niiccoo2/EINK-Phone/pic/4in2_Scale_2.bmp

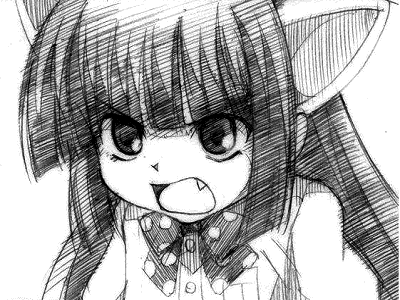
pic/4in2_Scale_2.bmp
