niiccoo2/EINK-Phone/pic/4.2 m.bmp

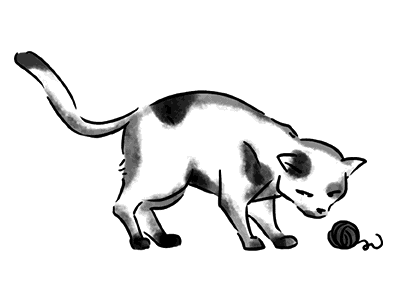
pic/4.2 m.bmp
