niiccoo2/EINK-Phone/pic/4.2-B.bmp

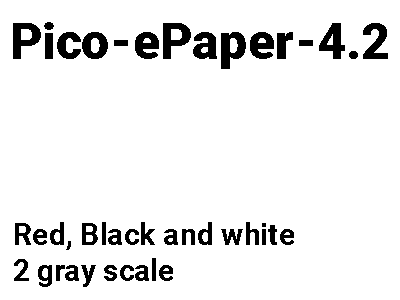
pic/4.2-B.bmp
