niiccoo2/EINK-Phone/pic/4.2-R.bmp

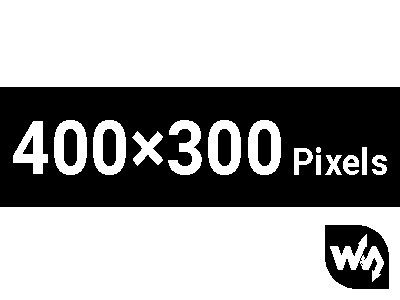
pic/4.2-R.bmp
