niiccoo2/EINK-Phone/pic/4in01-2.bmp

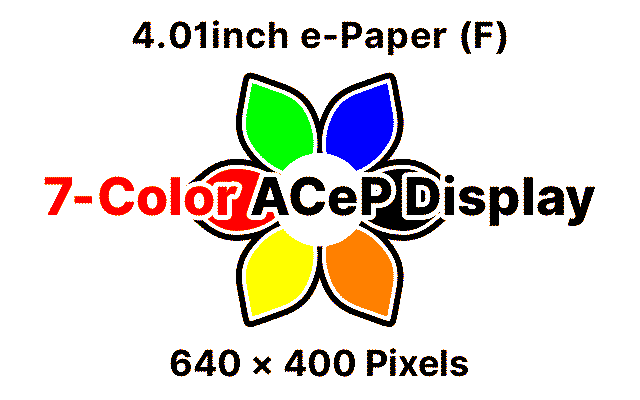
pic/4in01-2.bmp
