niiccoo2/EINK-Phone/pic/4in01-3.bmp

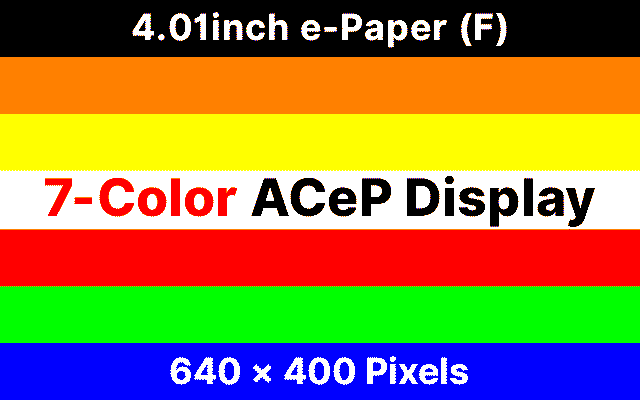
pic/4in01-3.bmp
