niiccoo2/EINK-Phone/pic/4in01-4.bmp

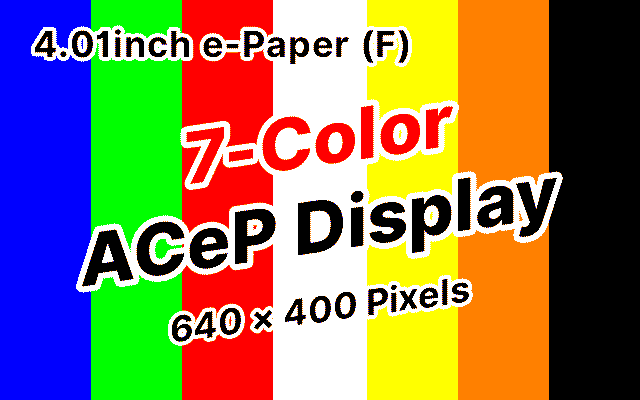
pic/4in01-4.bmp
