niiccoo2/EINK-Phone/pic/4in01f1.bmp

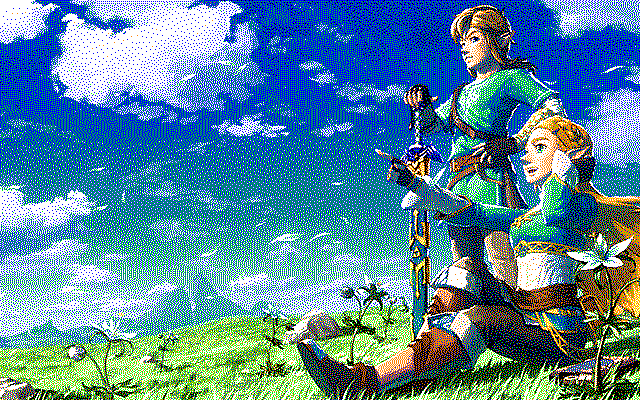
pic/4in01f1.bmp
