niiccoo2/EINK-Phone/pic/4in2.bmp

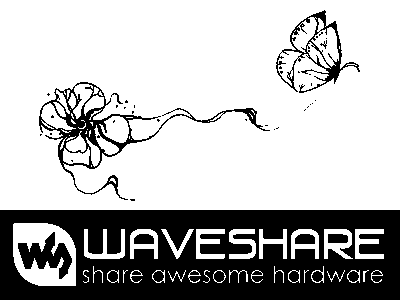
pic/4in2.bmp
