niiccoo2/EINK-Phone/pic/4in2_1.bmp

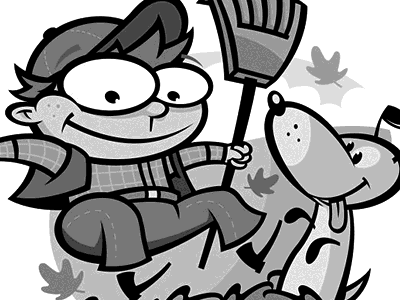
pic/4in2_1.bmp
