niiccoo2/EINK-Phone/pic/4in2_Pico.bmp

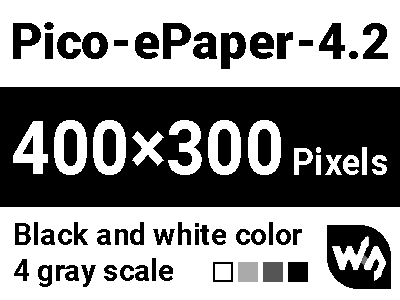
pic/4in2_Pico.bmp
