niiccoo2/EINK-Phone/pic/4in2_Scale.bmp

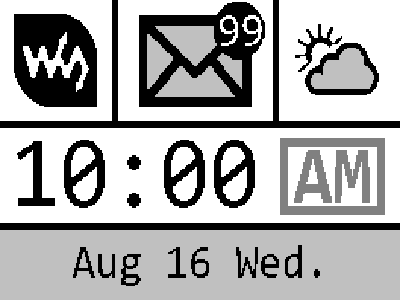
pic/4in2_Scale.bmp
