niiccoo2/EINK-Phone/pic/4in2b-r.bmp

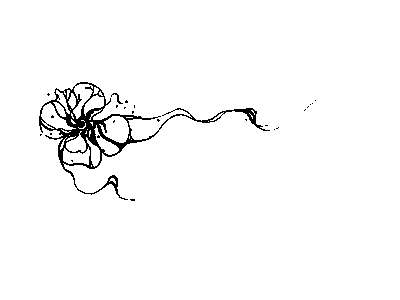
pic/4in2b-r.bmp
