niiccoo2/EINK-Phone/pic/4in2c-y.bmp

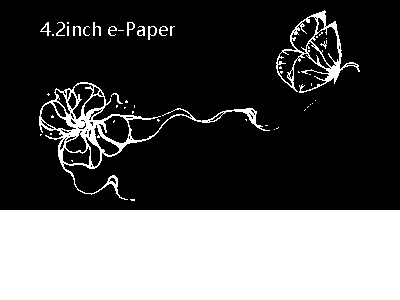
pic/4in2c-y.bmp
