niiccoo2/EINK-Phone/pic/4in26_Scale.bmp

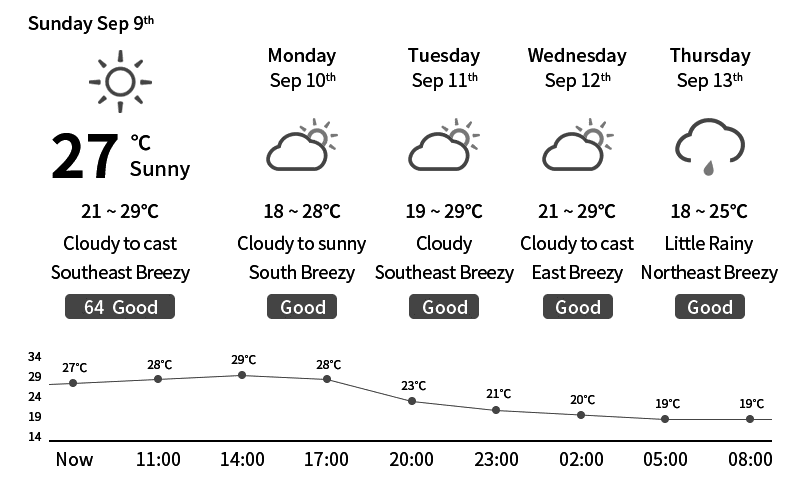
pic/4in26_Scale.bmp
