niiccoo2/EINK-Phone/pic/4in37g0.jpg

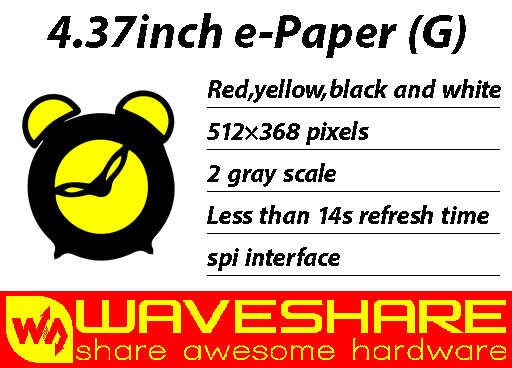
pic/4in37g0.jpg
