niiccoo2/EINK-Phone/pic/image.bmp

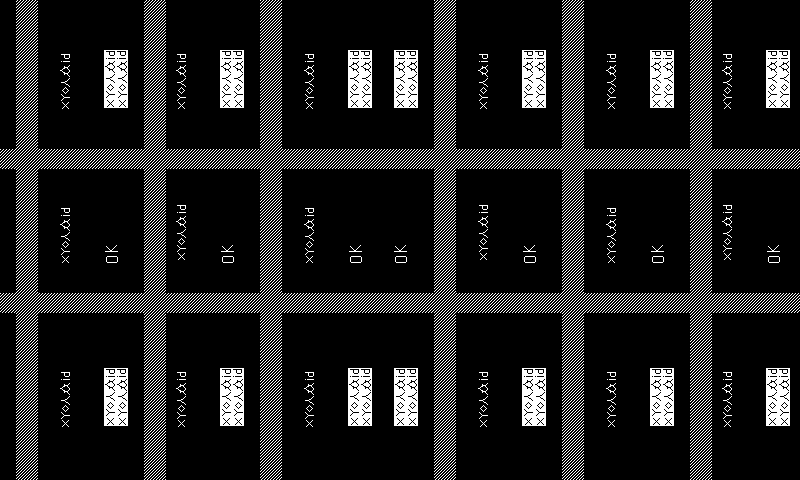
pic/image.bmp
