niiccoo2/EINK-Phone/pic/image_black.bmp

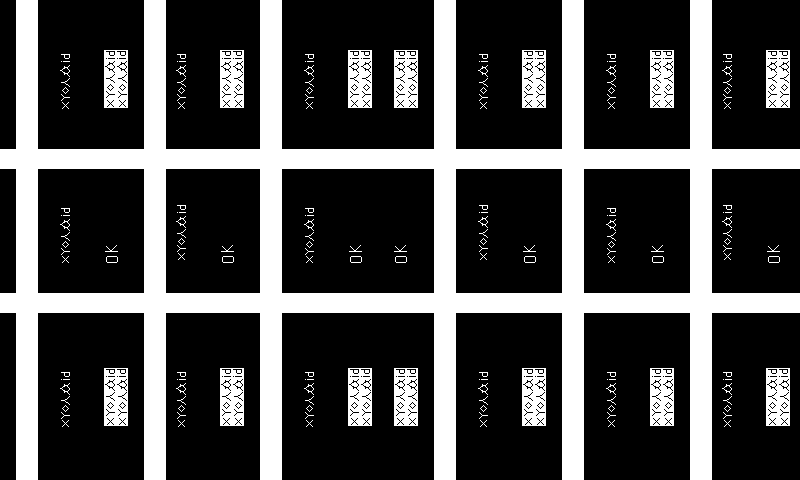
pic/image_black.bmp
