niiccoo2/EINK-Phone/pic/image_red.bmp

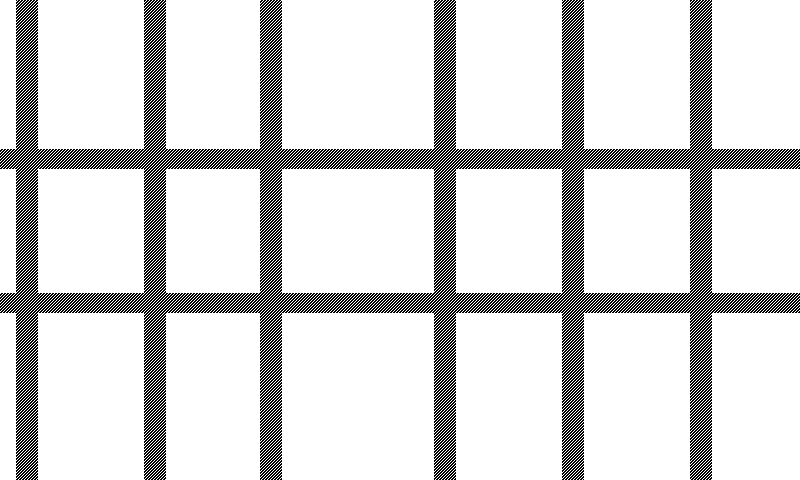
pic/image_red.bmp
